mbparks/BuildingAutomationProject/Hardware/HuzzahBoard/HuzzahBoard.sch

## EAGLE design Hardware/HuzzahBoard/HuzzahBoard.sch (2017-06-08)

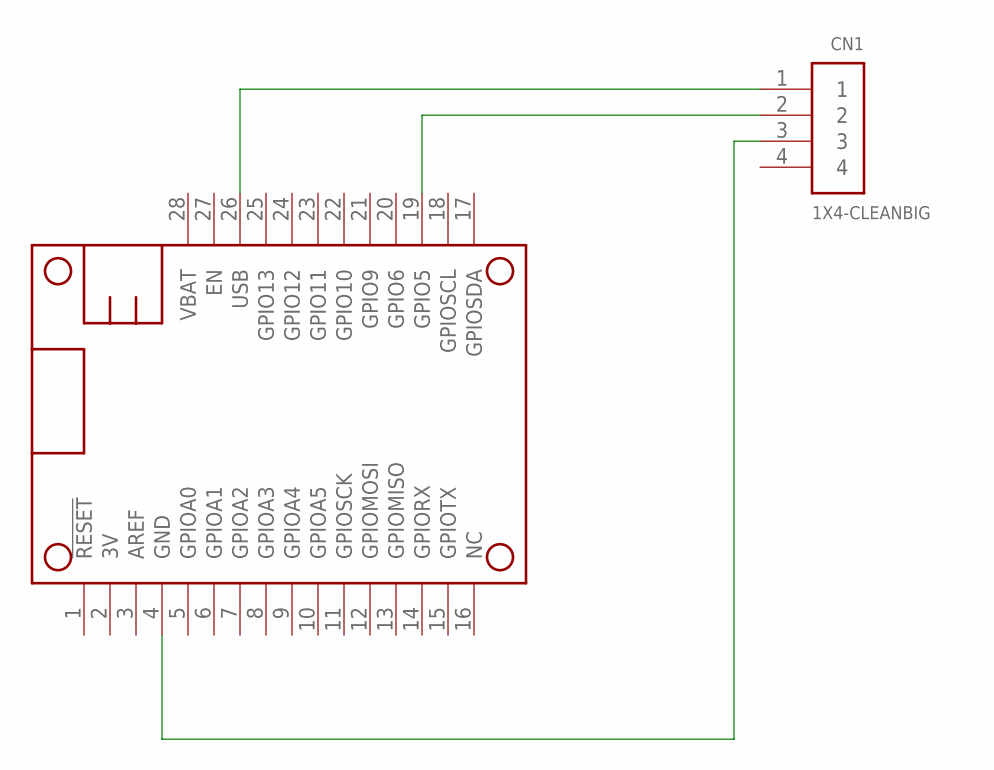
[picture p7: schematic HuzzahBoard.sch]

Parts:
CN1: 1X4-CLEANBIG; 1X04-CLEANBIG
MS1: FEATHERWING_NODIM; FEATHERWING_DIM

Connections:
unnamed: CN1.3, MS1.4 (GND)
unnamed: CN1.2, MS1.19 (GPIO5)
USB: CN1.1, MS1.26 (USB)
